Damov/esp32_weather_forecast_screen/images/location-cyrillic-uk.png

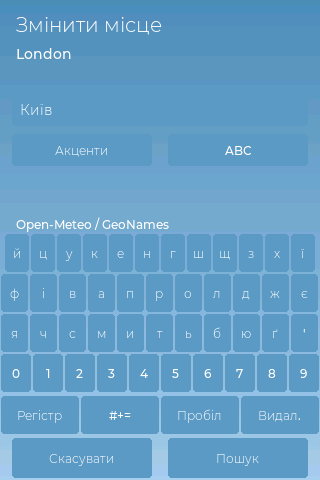
images/location-cyrillic-uk.png
