Damov/esp32_weather_forecast_screen/firmware/src/theme.rs

// ============================================================================= //
// File          : theme.rs                                                      //
// License       : MIT                                                           //
// Created       : 2026-10-04                                                    //
// Last modified : 2026-10-04                                                    //
// Author        : Daniel Kharlamov                                              //
// Last editor   : Daniel Kharlamov <daniel.kharlamov@googlemail.com>            //
// ============================================================================= //
//                                                                               //
// Summary:                                                                      //
// --------                                                                      //
// Shared UI colours, backgrounds, and bitmap font rendering.                    //
//                                                                               //
// Module:                                                                       //
// -------                                                                       //
// Defines the interface palette, gradient backgrounds, rounded panels, and      //
// backdrop blending. Renders proportional antialiased bitmap fonts with kerning //
// and Unicode glyph lookup, and provides text clipping and wrapping. Font       //
// assets retain their own licences and attribution notices.                     //
// ============================================================================= //

//! UI colours and small, shared proportional-font rendering helpers.
use embedded_graphics::{
    pixelcolor::{Rgb565, Rgb888},
    prelude::*,
    primitives::{PrimitiveStyle, Rectangle, RoundedRectangle},
};

// Solid background colour behind current weather and forecast tables. This fixed value is shared by
// the operations below.
pub const WEATHER_CARD: Rgb565 = rgb(0x397ca8);
// Solid background colour shared by interactive controls. This fixed value is shared by the
// operations below.
pub const PANEL: Rgb565 = rgb(0x5e9bc8);
// Primary foreground colour for readable labels. This fixed value is shared by the operations
// below.
pub const TEXT: Rgb565 = rgb(0xffffff);
// Secondary foreground colour used for less prominent content. This fixed value is shared by the
// operations below.
pub const SECONDARY: Rgb565 = rgb(0xe4ffff);
// Subdued colour used to distinguish disabled or secondary text. This fixed value is shared by the
// operations below.
pub const MUTED: Rgb565 = rgb(0xb9ecff);
// Shared four-pixel corner radius for interface panels. This fixed value is shared by the
// operations below.
pub const RADIUS: u32 = 4;

/// Converts a packed 24-bit RGB colour to rounded RGB565 channel values.
///
/// # Arguments
///
/// * `hex` (`u32`) - Packed 0xRRGGBB colour; bits above the low 24 are ignored.
///
/// # Returns
///
/// `Rgb565` - RGB565 colour using the low 24 bits of the supplied value.
pub const fn rgb(hex: u32) -> Rgb565 {
    // Construct the value from the supplied configuration or coordinates for use by the surrounding
    // operation.
    Rgb565::new(
        ((((hex >> 16) & 255) * 31 + 127) / 255) as u8,
        ((((hex >> 8) & 255) * 63 + 127) / 255) as u8,
        (((hex & 255) * 31 + 127) / 255) as u8,
    )
}
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
